CJA798/UNCA-IEEE/Collection/new_ducks/Pics/1676331447.jpg

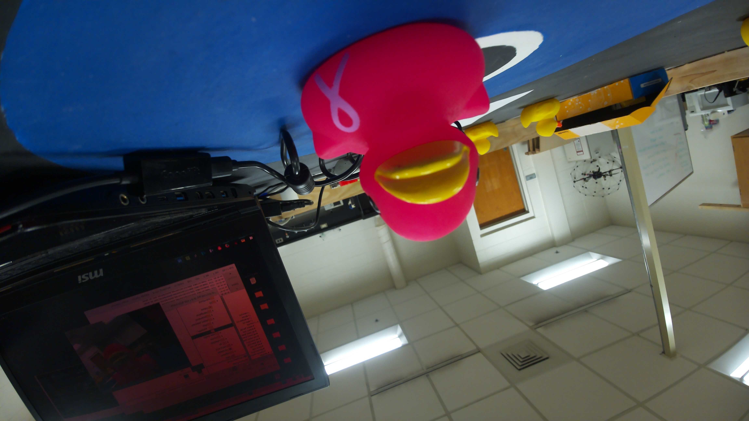
Collection/new_ducks/Pics/1676331447.jpg
