CJA798/UNCA-IEEE/WORKING ASSEMBLY/MK7.1 IEEE BOT/Steel 90 degree MK5.SLDPRT

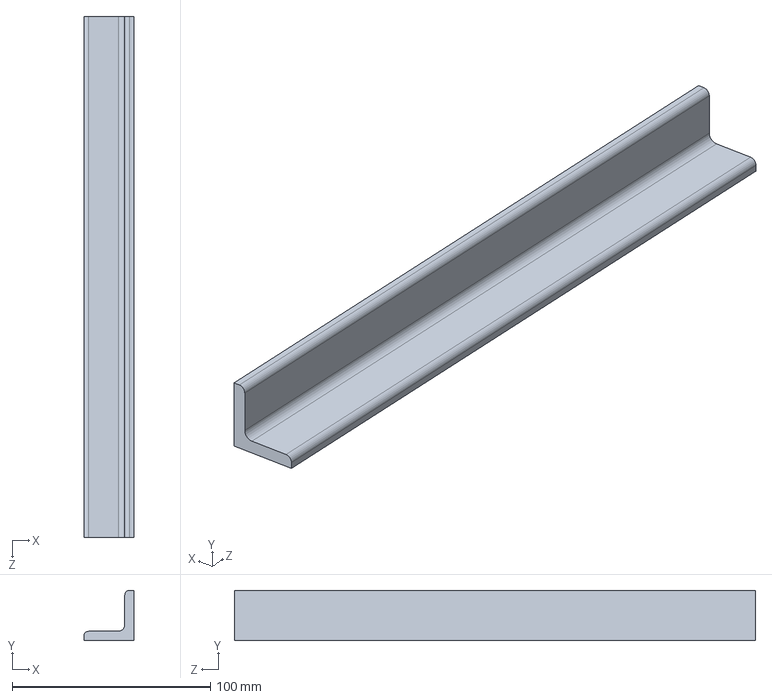
[picture p24: CAD file, 2023-04-08]
WORKING ASSEMBLY/MK7.1 IEEE BOT/Steel 90 degree MK5.SLDPRT
25.4 x 25.4 x 263.1 mm
