CJA798/UNCA-IEEE/WORKING ASSEMBLY/MK7.1 IEEE BOT/Omniwheel Hub.SLDPRT

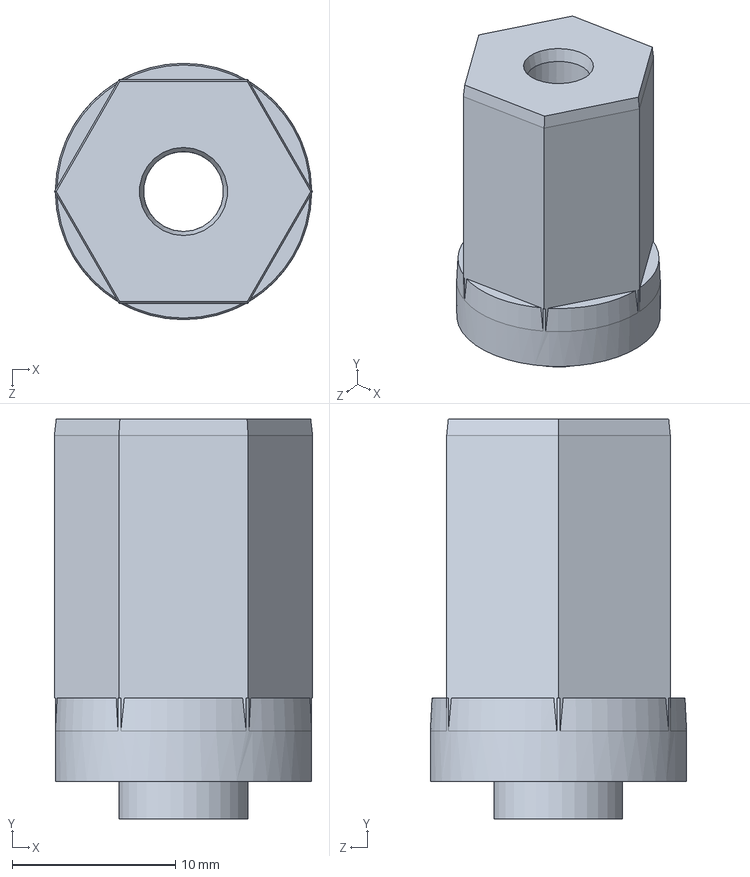
[picture p25: CAD file, 2023-04-08]
WORKING ASSEMBLY/MK7.1 IEEE BOT/Omniwheel Hub.SLDPRT
15.8 x 24.5 x 15.7 mm
