CJA798/UNCA-IEEE/WORKING ASSEMBLY/MK7.1 IEEE BOT/twist_inside_plate.STEP

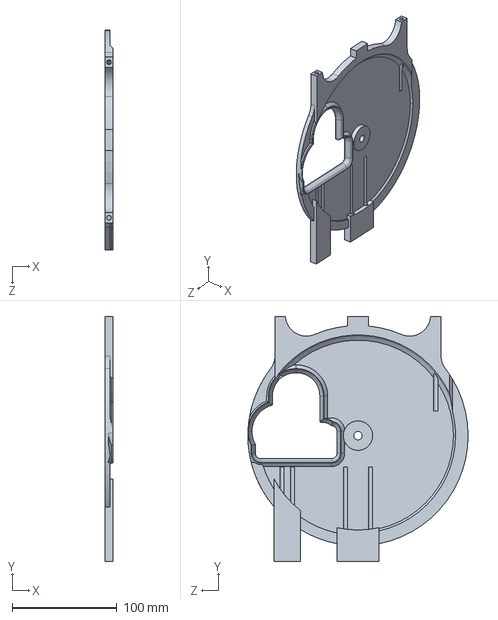
[picture p26: CAD file, 2023-04-08]
WORKING ASSEMBLY/MK7.1 IEEE BOT/twist_inside_plate.STEP
8.00 x 233.6 x 210.0 mm
