CJA798/UNCA-IEEE/WORKING ASSEMBLY/MK7.1 IEEE BOT/Bearing Slider.SLDPRT

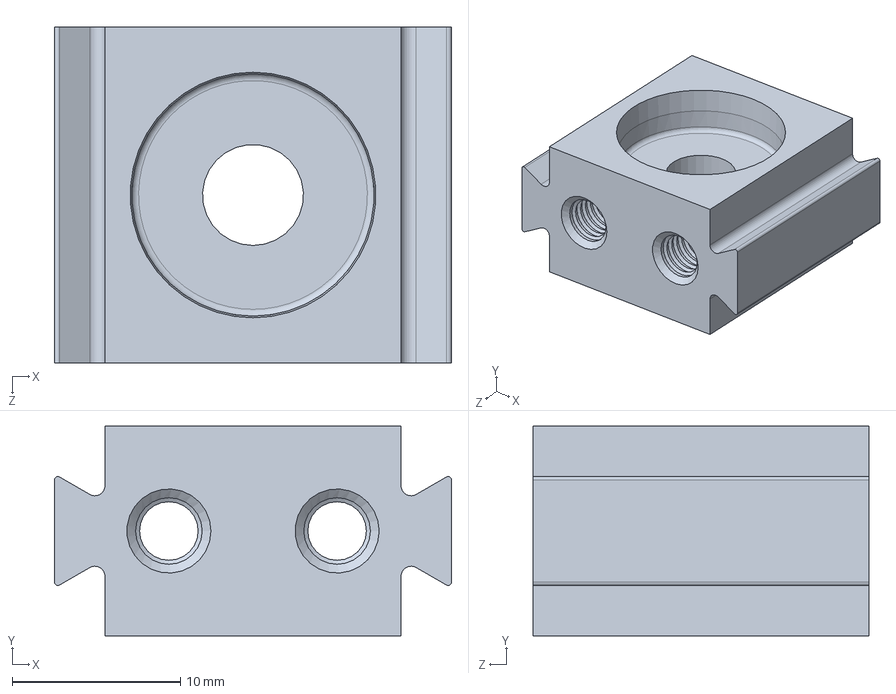
[picture p27: CAD file, 2023-04-08]
WORKING ASSEMBLY/MK7.1 IEEE BOT/Bearing Slider.SLDPRT
23.6 x 12.5 x 20.0 mm
