CJA798/UNCA-IEEE/WORKING ASSEMBLY/MK7.1 IEEE BOT/TOF sensor mount.SLDPRT

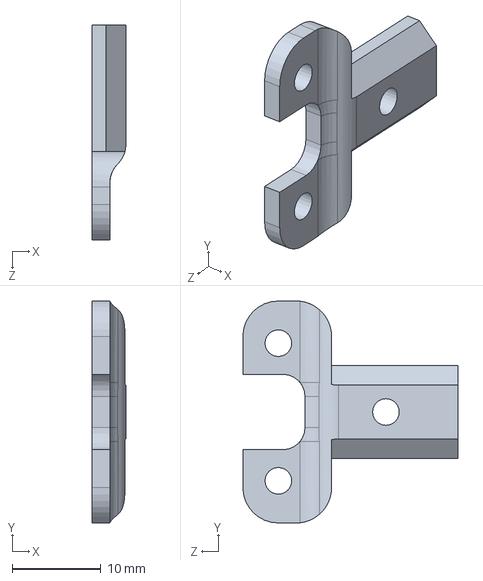
[picture p28: CAD file, 2023-04-08]
WORKING ASSEMBLY/MK7.1 IEEE BOT/TOF sensor mount.SLDPRT
3.80 x 25.0 x 24.2 mm
