CJA798/UNCA-IEEE/WORKING ASSEMBLY/MK7.1 IEEE BOT/Bottom Plate Bracket.SLDPRT

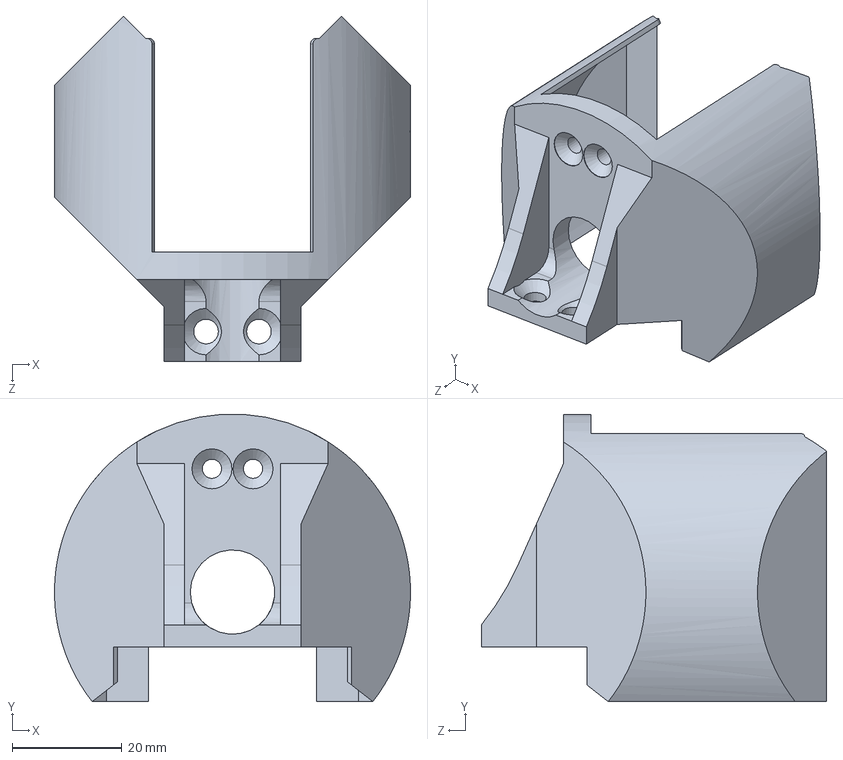
[picture p29: CAD file, 2023-04-08]
WORKING ASSEMBLY/MK7.1 IEEE BOT/Bottom Plate Bracket.SLDPRT
65.0 x 52.4 x 63.1 mm
