CJA798/UNCA-IEEE/WORKING ASSEMBLY/MK7.1 IEEE BOT/2in 14mm omniwheel-MK5.SLDPRT

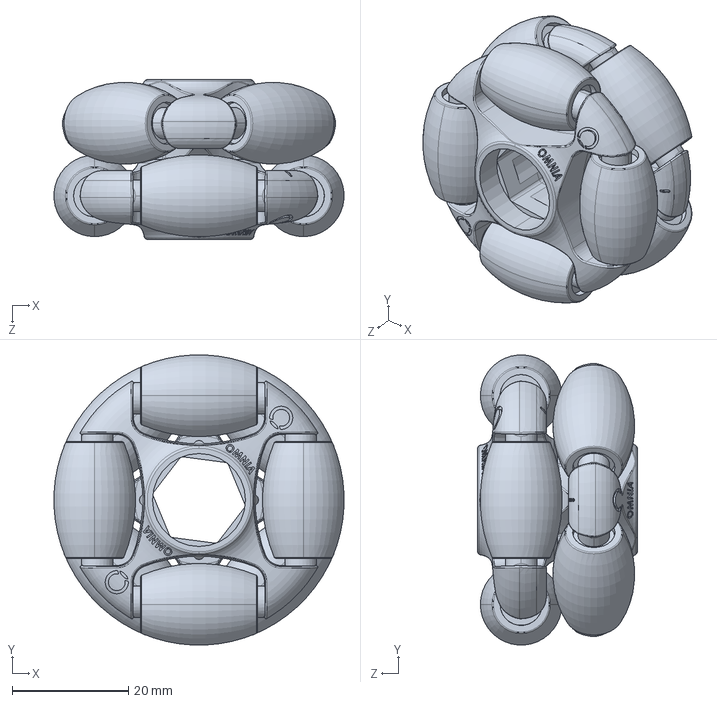
[picture p30: CAD file, 2023-04-08]
WORKING ASSEMBLY/MK7.1 IEEE BOT/2in 14mm omniwheel-MK5.SLDPRT
49.9 x 49.9 x 27.5 mm
