CJA798/UNCA-IEEE/WORKING ASSEMBLY/MK7.1 IEEE BOT/6mm G2T Pully Gear.SLDPRT

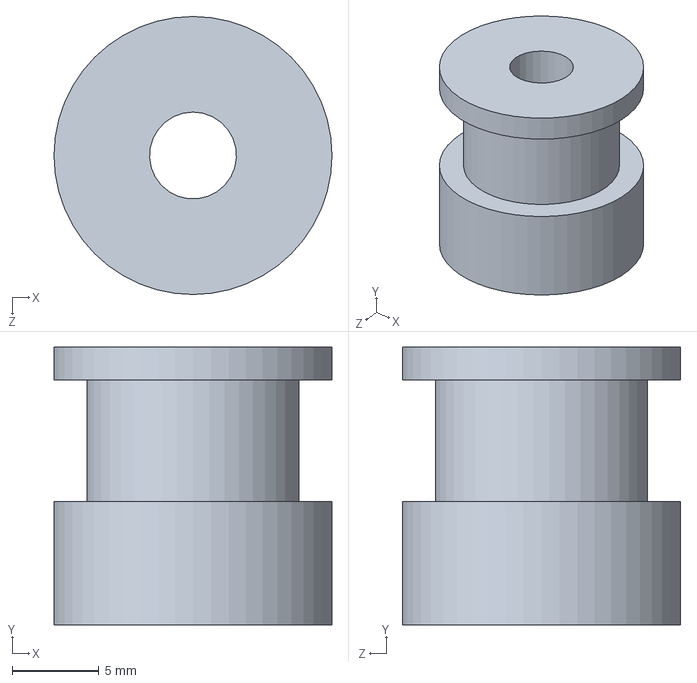
[picture p31: CAD file, 2023-04-08]
WORKING ASSEMBLY/MK7.1 IEEE BOT/6mm G2T Pully Gear.SLDPRT
16.0 x 16.0 x 16.0 mm
