CJA798/UNCA-IEEE/WORKING ASSEMBLY/MK7.1 IEEE BOT/Nema14Pancake Stepper.SLDPRT

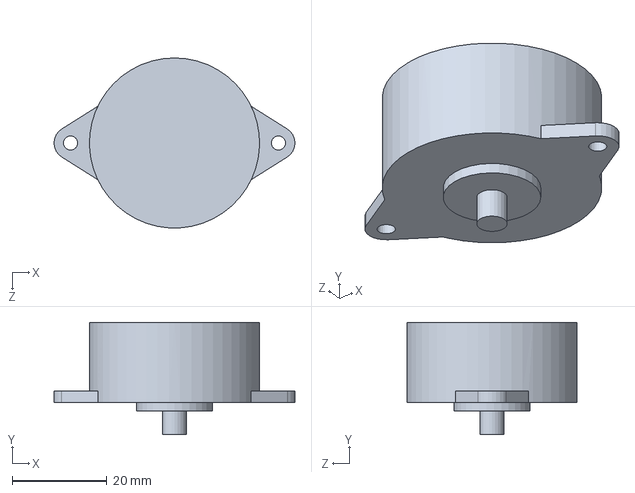
[picture p32: CAD file, 2023-04-08]
WORKING ASSEMBLY/MK7.1 IEEE BOT/Nema14Pancake Stepper.SLDPRT
51.0 x 23.8 x 36.0 mm
