CJA798/UNCA-IEEE/Navigation/LOCOMOTION V4!/include/macros.h

// NO MAGIC NUMBERS!!!! KEEP CARLSON PROUD!!!!!!!!!
//--------STATES--------------------------------------------------------------------
#define IDLE (0)
#define TRANSLATING (1)
#define ROTATING (2)
#define COMPLEX_MOVE (3)

//--------ADDRESSES AND OTHER CONSTANTS---------------------------------------------
// Addresses for the sensors
#define L1X1_ADDRESS 0x29
#define L1X2_ADDRESS 0x2B
#define L1X3_ADDRESS 0x2D
#define L1X4_ADDRESS 0x2F
#define LOX1_ADDRESS 0x31
#define LOX2_ADDRESS 0x33
#define LOX3_ADDRESS 0x35
#define LOX4_ADDRESS 0x37

#define RESET_TIME 100

//-------KINEMATICS CONSTANTS-------------------------------------------------------
#define ONE_OVR_RT_2 (0.707106)     // (1/sqrt(2))
#define STEPS_PER_ROTATION (400)    // (200steps per rotation) * (16 microsteps per step)
#define STEPS_PER_CM (25.46)        // Steps per inch in arclength any given wheel travels = StepsPerWheelRotation/WheelCircumference
#define WHEEL_RADIUS (2.5)          // Radius of wheel(cm) (1in)
#define STEPS_PER_BOT_RAD (1315)    // = ((BotCircumference*StepsPerCm*)/(2*Pi))*3 (gear ratio)
#define STEPS_PER_DIST_MULT (51.32) // = (1/sqrt(2))*StepsPerCM*3 (gear ratio) WAS 54.02; UPPED TO
#define MAX_MTR_SPEED (800)         // Steps/s maximum is 300000
#define MAX_MTR_ACCEL (400)         // Steps/s^2 skips at around 15000

#define NORTH_WALL (91)
#define SOUTH_WALL (0)
#define EAST_WALL (99)
#define WEST_WALL (-99)
#define NORTH ('N')
#define SOUTH ('S')
#define EAST ('E')
#define WEST ('W')
//-------Navigation Stuff------------------------------------------------------------
#define mtx_type float // Matrix type definition
#define BLOCKING (1)
#define NON_BLOCKING (0)
#define ROTATIONAL (1)
#define LINEAR (0)
#define MOTOR_SATURATION_SPEED (4000)
#define COMPLEX_MOVE_ACCEL (10000)
#define INPUT_VECT_PROPORTIONAL_RADUIS (1)
#define MOVE_TIME_PERIOD (200) // ms
#define PROPORTIONAL_DIVIDER (.1)
