CJA798/UNCA-IEEE/Collection/new_ducks/c_test/FlipperPlatform.h

////////////////////////////////////////////////////////////////////////////////
//  Description: This file contains the FlipperPlatform class
//
//  Modified: Carlos Anzola (27 Mar 2023)
////////////////////////////////////////////////////////////////////////////////
//  Ideally, the rotation servo ratates until the object is oriented.
//  Then, the flip servo flips the platform, sending the object to the
//  elevator platform.
//  If there is more than one object, the clean servo clears the platform.
////////////////////////////////////////////////////////////////////////////////

#include <Servo.h>
#include "macros.h"

enum class Flipper_Platform_Status {
  NO_OBJECTS_IN_PLATFORM,
  UNORIENTED_OBJECT,
  ORIENTED_OBJECT,
  FLIPPING_OBJECT,
  FLIPPER_PLATFORM_ERROR_MORE_THAN_ONE_OBJECT,
  FLIPPER_PLATFORM_ERROR_UNKNOWN
};


class FlipperPlatform {
  private:
    // Private attributes
    Servo rotationServo;
    Servo flipServo;
    Servo clearServo;

    // Private helper function to wait for a certain amount of time
    void wait(unsigned long duration) {
      unsigned long startTime = millis();
      while (millis() - startTime < duration) {
        // Do nothing while waiting
      }
    }


  public:
    // Public attributes
    Flipper_Platform_Status status;
    int currentAngle;
    int numObjects;

  // Constructor to initialize the class attributes    
    FlipperPlatform(int rotationServoPin, int flipServoPin, int clearServoPin) {
      status = Flipper_Platform_Status::NO_OBJECTS_IN_PLATFORM;
      currentAngle = 0;
      numObjects = 0;      
      rotationServo.attach(rotationServoPin);
      rotationServo.writeMicroseconds(1500);
      flipServo.attach(flipServoPin);
      clearServo.attach(clearServoPin);
    }

    void rotatePlatform() {
      rotationServo.writeMicroseconds(1600);
    }

    void stopRotation(){
      rotationServo.writeMicroseconds(1500);      
    }

    void flipPlatform(/*ElevatorPlatform& elevatorPlatform*/) {
      //while(elevatorPlatform.status == READY){}
      status = Flipper_Platform_Status::FLIPPING_OBJECT;
      flipServo.write(80);
      wait(2000);
      flipServo.write(10);
      wait(2000);
    }

    void clearPlatform() {
      clearServo.write(80);
      wait(2000);
      clearServo.write(10);
      wait(2000);
    }

    Flipper_Platform_Status getStatus(Flipper_Platform_Status state) {
      return status;
    }
    
    void setStatus(Flipper_Platform_Status state) {
      status = state;
    }

    int getCurrentAngle() {
      return currentAngle;
    }

    void setCurrentAngle(int angle) {
      currentAngle = angle;
    }

    int getNumObjects() {
      return numObjects;
    }

    void setNumObjects(int num) {
      numObjects = num;
    }

};
