CJA798/UNCA-IEEE/Collection/new_ducks/c_test/macros.h

////////////////////////////////////////////////////////////////////////////////
//  Description: This file contains the macros
//
//  Modified: Carlos Anzola (27 Feb 2023)
////////////////////////////////////////////////////////////////////////////////

#define TRUE 1
#define FALSE 0

#define BUILT_IN_LED_PIN 13
#define PINK_DUCK_PIN 2
#define YELLOW_DUCK_PIN 3
#define RED_PILLAR_PIN 4
#define GREEN_PILLAR_PIN 5
#define WHITE_PILLAR_PIN 6

#define ORIENTATION_SERVO_PIN 9

#define ROTATION_SERVO_PIN 10
#define FLIP_SERVO_PIN 11
#define CLEAR_SERVO_PIN 12

#define MAX_INPUT_SIZE 128
#define NO_INCOMING_DATA 0

#define DUCK 0
#define PILLAR 1

#define YELLOW_DUCK 0
#define PINK_DUCK 1
#define WHITE_PILLAR 2
#define GREEN_PILLAR 3
#define RED_PILLAR 4

#define YELLOW 0
#define PINK 1
#define WHITE 2
#define GREEN 3
#define RED 4
#define ALL 5

#define FIRST_YELLOW_DUCK 0
#define SECOND_YELLOW_DUCK 2

#define NO_STORAGE_AVAILABLE 15 // 4'b1111
#define FIRST_SLOT 0
#define SECOND_SLOT 1
#define THIRD_SLOT 2
#define FOURTH_SLOT 3   // whites
#define FIFTH_SLOT 4    // greens
#define SIXTH_SLOT 5    // red & green
#define BRACING_SLOT 6  // white

#define FIRST_POSITION 0
#define SECOND_POSITION 1

#define PUSH_IN 0
#define PUSH_OUT 1

#define CANT_ADD_ITEM 0
#define ITEM_ADDED 1

#define ITEM_REMOVED 0
#define CANT_REMOVE_ITEM 1




#define SMALL_BRACING 0
#define BIG_BRACING 1
