CJA798/UNCA-IEEE/Collection/collection_system/utils.py

# Copyright 2021 The TensorFlow Authors. All Rights Reserved.
#
# Licensed under the Apache License, Version 2.0 (the "License");
# you may not use this file except in compliance with the License.
# You may obtain a copy of the License at
#
#     http://www.apache.org/licenses/LICENSE-2.0
#
# Unless required by applicable law or agreed to in writing, software
# distributed under the License is distributed on an "AS IS" BASIS,
# WITHOUT WARRANTIES OR CONDITIONS OF ANY KIND, either express or implied.
# See the License for the specific language governing permissions and
# limitations under the License.
"""Utility functions to display the pose detection results."""

import cv2
import numpy as np
from math import atan2, cos, sin, sqrt, pi
from tflite_support.task import processor

_MARGIN = 10  # pixels
_ROW_SIZE = 10  # pixels
_FONT_SIZE = 1
_FONT_THICKNESS = 1
_TEXT_COLOR = (0, 0, 255)  # red


def visualize(
    image: np.ndarray,
    detection_result: processor.DetectionResult,
) -> np.ndarray:
  """Draws bounding boxes on the input image and return it.

  Args:
    image: The input RGB image.
    detection_result: The list of all "Detection" entities to be visualize.

  Returns:
    Image with bounding boxes.
  """
  for detection in detection_result:
    # Draw bounding_box
    bbox = detection.bounding_box
    #start_point = bbox.origin_x, bbox.origin_y
    #end_point = bbox.origin_x + bbox.width, bbox.origin_y + bbox.height
    #cv2.rectangle(image, start_point, end_point, _TEXT_COLOR, 3)

    # Draw label and score
    category = detection.categories[0]
    category_name = category.category_name
    probability = round(category.score, 2)
    result_text = category_name + ' (' + str(probability) + ')'
    text_location = (_MARGIN + bbox.origin_x,
                     _MARGIN + _ROW_SIZE + bbox.origin_y)
    cv2.putText(image, result_text, text_location, cv2.FONT_HERSHEY_PLAIN,
                _FONT_SIZE, _TEXT_COLOR, _FONT_THICKNESS)

  return image


def drawAxis(img, p_, q_, color, scale):
  p = list(p_)
  q = list(q_)
 
  ## [visualization1]
  angle = atan2(p[1] - q[1], p[0] - q[0]) # angle in radians
  hypotenuse = sqrt((p[1] - q[1]) * (p[1] - q[1]) + (p[0] - q[0]) * (p[0] - q[0]))
 
  # Here we lengthen the arrow by a factor of scale
  q[0] = p[0] - scale * hypotenuse * cos(angle)
  q[1] = p[1] - scale * hypotenuse * sin(angle)
  cv2.line(img, (int(p[0]), int(p[1])), (int(q[0]), int(q[1])), color, 3, cv2.LINE_AA)
 
  # create the arrow hooks
  p[0] = q[0] + 9 * cos(angle + pi / 4)
  p[1] = q[1] + 9 * sin(angle + pi / 4)
  cv2.line(img, (int(p[0]), int(p[1])), (int(q[0]), int(q[1])), color, 3, cv2.LINE_AA)
 
  p[0] = q[0] + 9 * cos(angle - pi / 4)
  p[1] = q[1] + 9 * sin(angle - pi / 4)
  cv2.line(img, (int(p[0]), int(p[1])), (int(q[0]), int(q[1])), color, 3, cv2.LINE_AA)
  ## [visualization1]


def getOrientation(pts, img, x, y):
  ## [pca]
  # Construct a buffer used by the pca analysis
  sz = len(pts)
  data_pts = np.empty((sz, 2), dtype=np.float64)
  for i in range(data_pts.shape[0]):
    data_pts[i,0] = pts[i,0,0]
    data_pts[i,1] = pts[i,0,1]
 
  # Perform PCA analysis
  mean = np.empty((0))
  mean, eigenvectors, eigenvalues = cv2.PCACompute2(data_pts, mean)
 
  # Store the center of the object
  cntr = (int(mean[0,0])+x, int(mean[0,1])+y)
  ## [pca]
 
  ## [visualization]
  # Draw the principal components
  cv2.circle(img, cntr, 3, (255, 0, 255), 2)
  p1 = (cntr[0] + 0.02 * eigenvectors[0,0] * eigenvalues[0,0], cntr[1] + 0.02 * eigenvectors[0,1] * eigenvalues[0,0])
  p2 = (cntr[0] - 0.02 * eigenvectors[1,0] * eigenvalues[1,0], cntr[1] - 0.02 * eigenvectors[1,1] * eigenvalues[1,0])
  drawAxis(img, cntr, p1, (255, 255, 0), 5)
  drawAxis(img, cntr, p2, (0, 0, 255), 5)
 
  angle = atan2(eigenvectors[0,1], eigenvectors[0,0]) # orientation in radians
  angle = int(abs(np.rad2deg(angle)))
  label = "Angle: " + str(angle)
  cv2.putText(img, label, (cntr[0], cntr[1]), cv2.FONT_HERSHEY_SIMPLEX, 0.5, (255,0,255), 1, cv2.LINE_AA)
 
  return angle
 
