CJA798/UNCA-IEEE/Collection/new_ducks/c_test/ElevatorPlatform.h

////////////////////////////////////////////////////////////////////////////////
//  Description: This file contains the ElevatorPlatform class
//
//  Modified: Carlos Anzola (27 Mar 2023)
////////////////////////////////////////////////////////////////////////////////

#include <Servo.h>
#include "macros.h"
